HelsinkiHacklab/DPS5020/schema/schema.sch

## KiCad design schema/schema.sch (2022-01-13)

Schematic: schema.sch

Parts:
F1: Fuse
J1, J4: BananaSocket,Red
J2, J5: BananaSocket,black
J3: Jack-DC
SW1: SW_DPST
U1: DPS5020
